jes1510/mendel_remix/parts/Cable_Chain/cc_150x8.stl

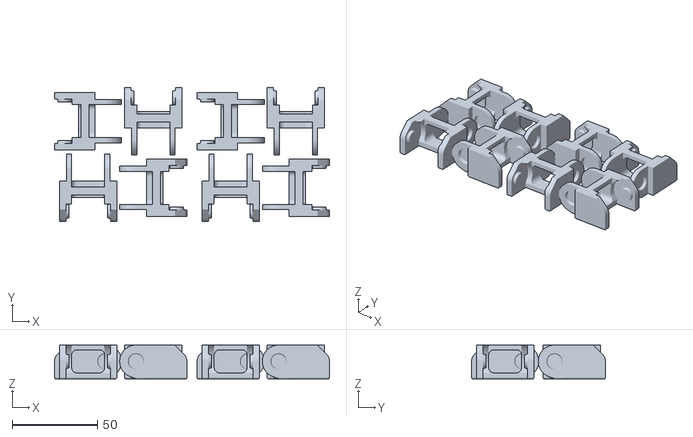
[picture p15: CAD file, 2015-03-10]
parts/Cable_Chain/cc_150x8.stl
161.2 x 78.5 x 19.9
