jes1510/mendel_remix/parts/case/Ramps_1.4_Mountable_Case/case_b.stl

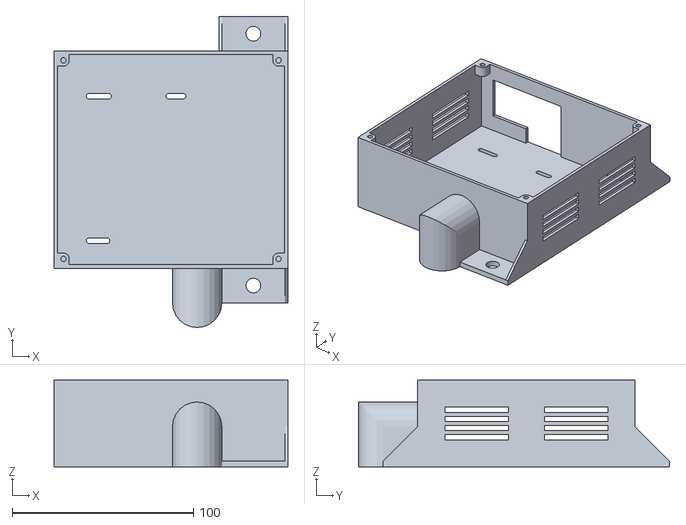
[picture p16: CAD file, 2015-03-10]
parts/case/Ramps_1.4_Mountable_Case/case_b.stl
129.1 x 171.8 x 48.0
