jes1510/mendel_remix/parts/electronics/Enclosure_RaspberryPi__ramps/Deckel_Fan.STL

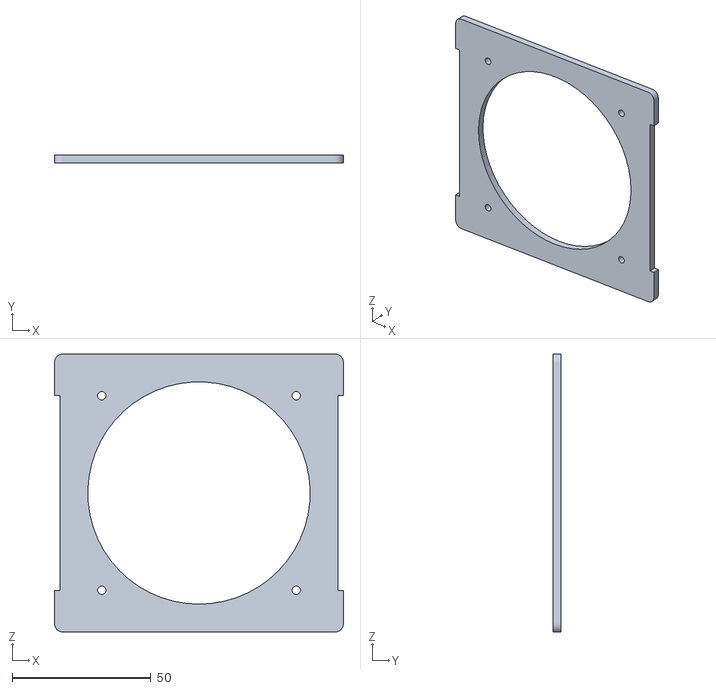
[picture p17: CAD file, 2014-10-29]
parts/electronics/Enclosure_RaspberryPi__ramps/Deckel_Fan.STL
104.0 x 3.00 x 100.0
