jes1510/mendel_remix/parts/enclosure/front_mid_brackets/front_mid_brackets_fixed.stl

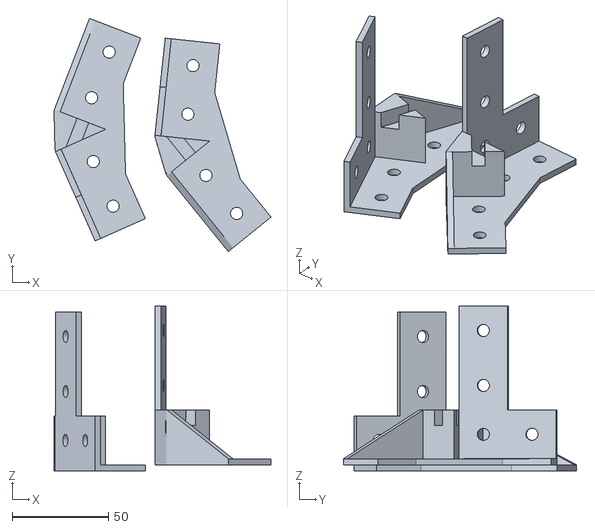
[picture p18: CAD file, 2015-06-04]
parts/enclosure/front_mid_brackets/front_mid_brackets_fixed.stl
112.8 x 121.3 x 85.7
