jes1510/mendel_remix/parts/enclosure/new_brackets/right_B_fixed.stl

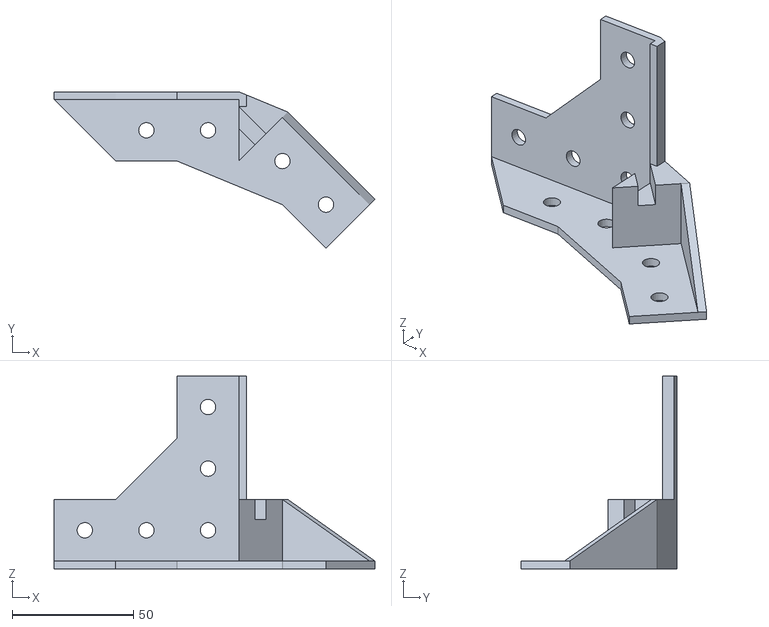
[picture p19: CAD file, 2015-06-04]
parts/enclosure/new_brackets/right_B_fixed.stl
132.3 x 64.5 x 79.4
