jes1510/mendel_remix/parts/enclosure/right_top_front_fixed.stl

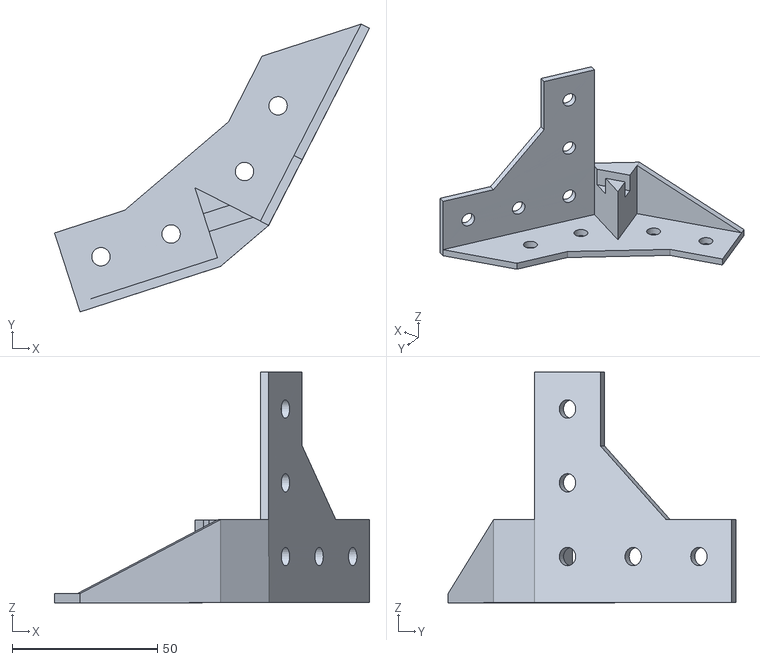
[picture p20: CAD file, 2015-06-04]
parts/enclosure/right_top_front_fixed.stl
108.5 x 99.1 x 79.4
