jes1510/mendel_remix/parts/enclosure/simple_brackets/sides_c.dxf

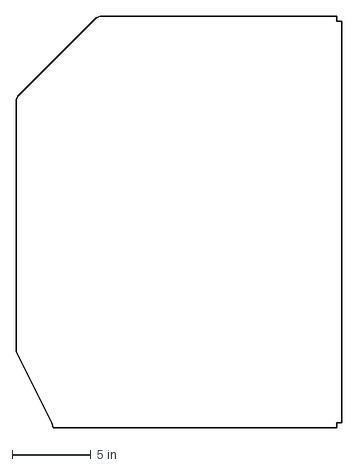
[picture p21: CAD file, 2015-06-04]
parts/enclosure/simple_brackets/sides_c.dxf
20.7 x 26.1 in
