jes1510/mendel_remix/parts/extruder_clamps.stl

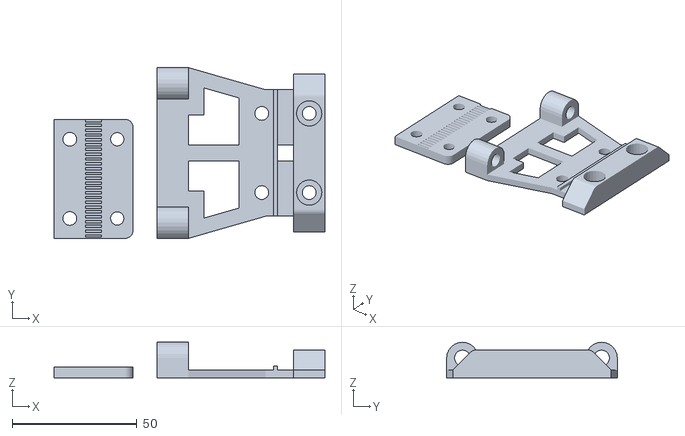
[picture p22: CAD file, 2015-03-10]
parts/extruder_clamps.stl
108.8 x 68.6 x 14.3
