jes1510/mendel_remix/parts/lcd_support/side.stl

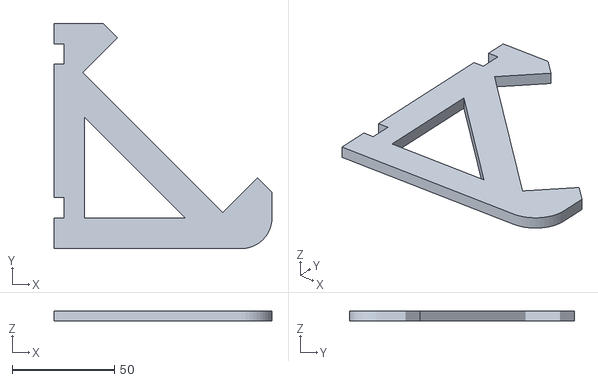
[picture p23: CAD file, 2014-11-15]
parts/lcd_support/side.stl
106.8 x 110.3 x 5.00
