jes1510/mendel_remix/parts/RAMP_14_Enclosure_Proven_to_fit/Case_Body.stl

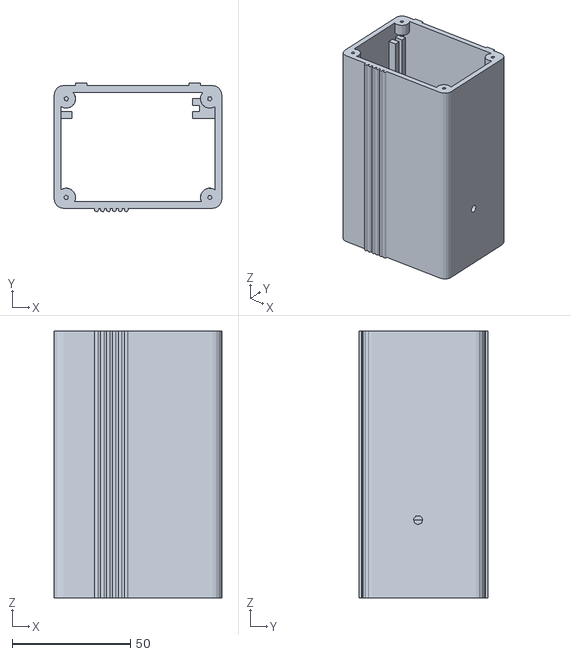
[picture p24: CAD file, 2014-11-15]
parts/RAMP_14_Enclosure_Proven_to_fit/Case_Body.stl
71.0 x 54.5 x 113.0
