jes1510/mendel_remix/xcablecarrier_brackets.dxf

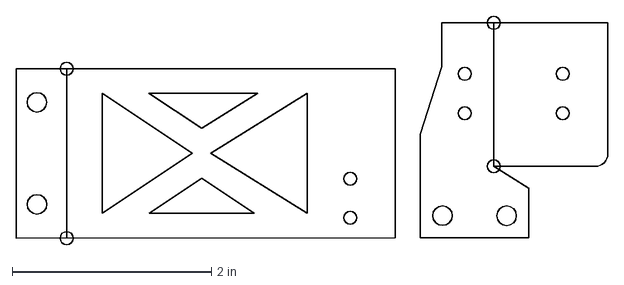
[picture p25: CAD file, 2015-03-10]
xcablecarrier_brackets.dxf
5.94 x 2.29 in
