jes1510/mendel_remix/parts/3DR_-_RepRapDiscount_Full_Graphic_Smart_Controller_case/3DR_Pablo_LCD_adapter.stl

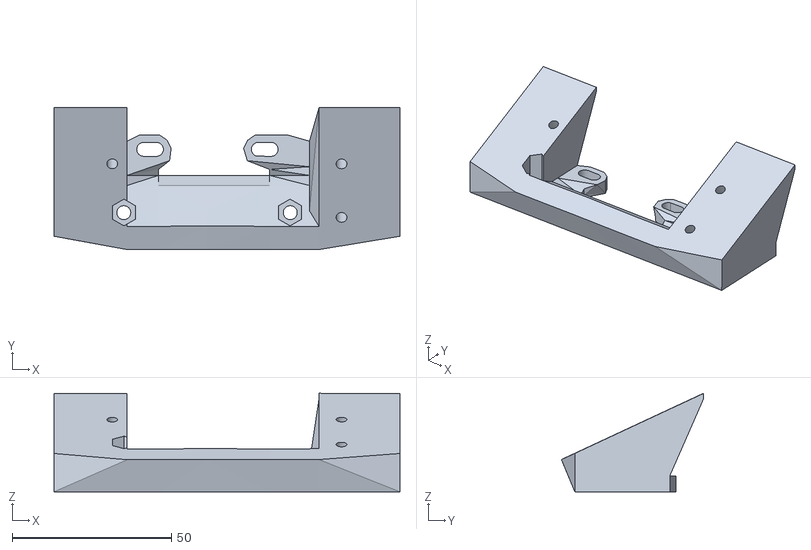
[picture p26: CAD file, 2014-11-15]
parts/3DR_-_RepRapDiscount_Full_Graphic_Smart_Controller_case/3DR_Pablo_LCD_adapter.stl
108.6 x 44.6 x 30.9
