jes1510/mendel_remix/parts/Cable_Chain/CableChainEnds.stl

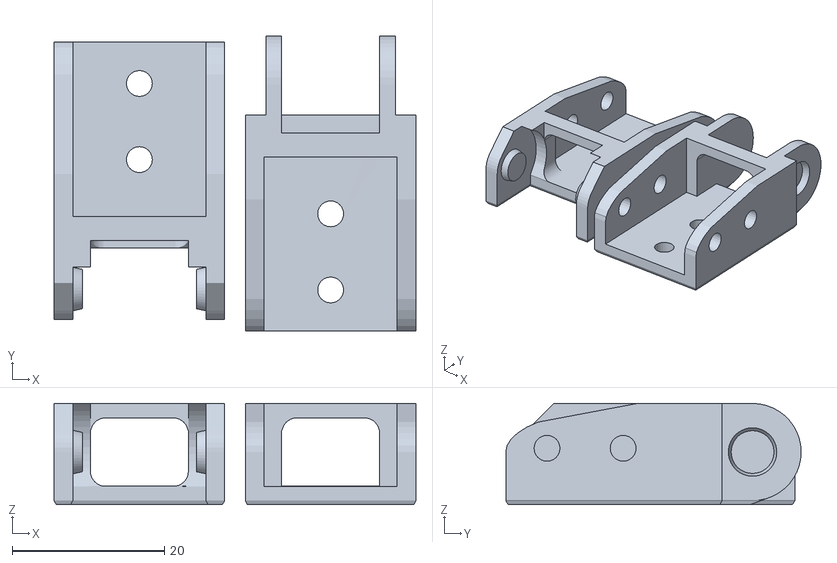
[picture p27: CAD file, 2014-11-15]
parts/Cable_Chain/CableChainEnds.stl
47.6 x 38.8 x 13.3
