jes1510/mendel_remix/parts/case/Ramps_1.4_Mountable_Case/Ramps_1.4_Mountable_Case06966831b87491ca3ae4c1595dea0038-Ramps_box_1-3_fan_cover.stl

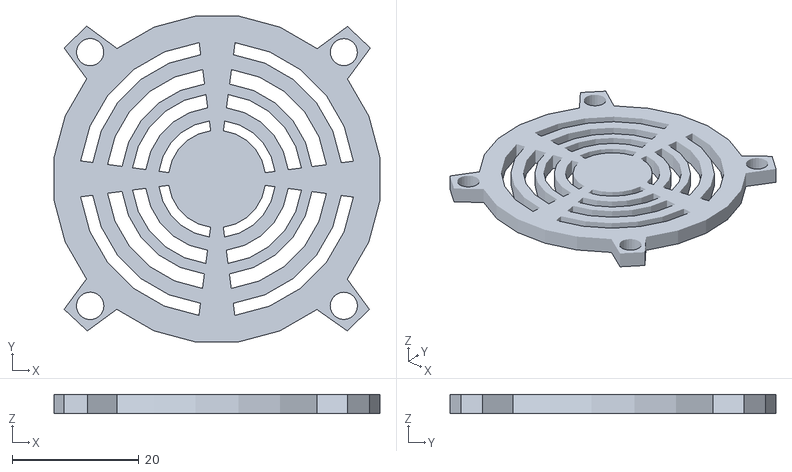
[picture p28: CAD file, 2015-03-10]
parts/case/Ramps_1.4_Mountable_Case/Ramps_1.4_Mountable_Case06966831b87491ca3ae4c1595dea0038-Ramps_box_1-3_fan_cover.stl
51.4 x 51.4 x 3.00
