jes1510/mendel_remix/parts/electronics/Enclosure_RaspberryPi__ramps/Schale.STL

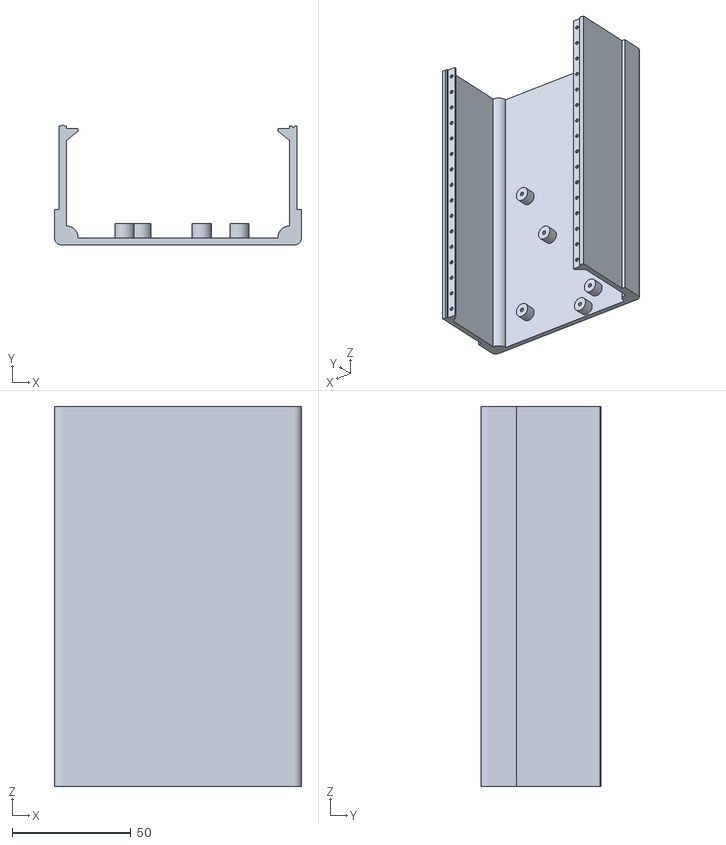
[picture p29: CAD file, 2014-10-29]
parts/electronics/Enclosure_RaspberryPi__ramps/Schale.STL
104.0 x 50.5 x 160.0
