jes1510/mendel_remix/parts/enclosure/front_mid_brackets/front_mid_L_Bracket.stl

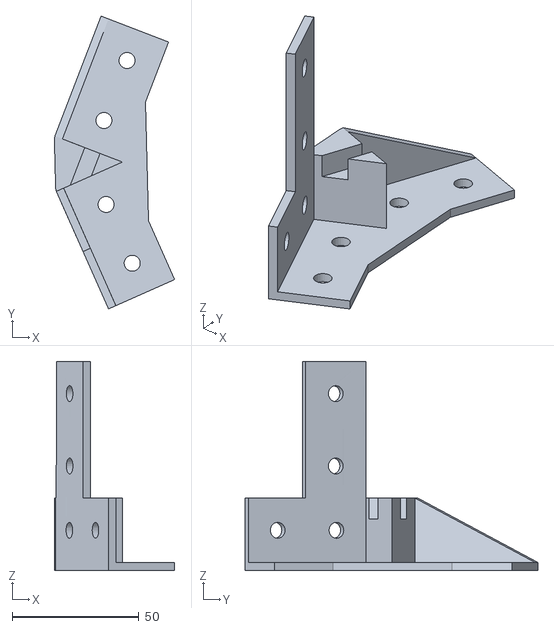
[picture p30: CAD file, 2015-06-04]
parts/enclosure/front_mid_brackets/front_mid_L_Bracket.stl
47.5 x 115.7 x 82.6
