jes1510/mendel_remix/parts/enclosure/new_brackets/right_A.stl

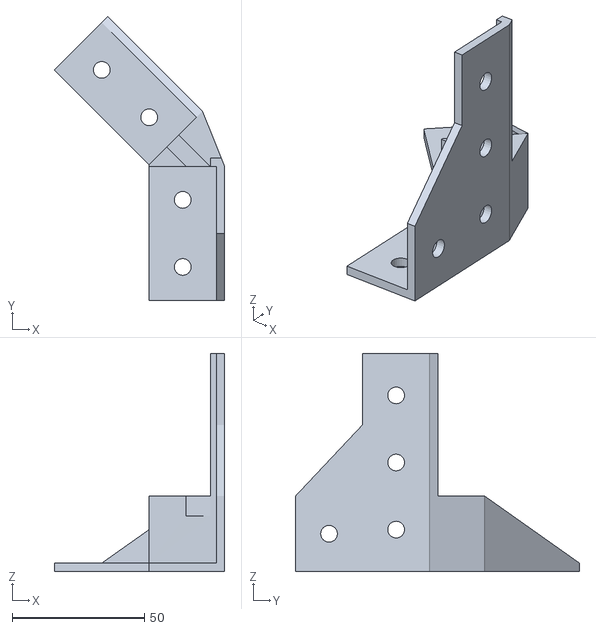
[picture p31: CAD file, 2015-06-04]
parts/enclosure/new_brackets/right_A.stl
64.5 x 107.5 x 82.6
