jes1510/mendel_remix/parts/enclosure/simple_brackets/sides.dxf

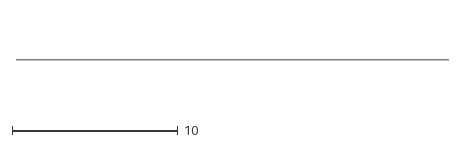
[picture p32: CAD file, 2015-06-04]
parts/enclosure/simple_brackets/sides.dxf
26.1 x 0.0455
