jes1510/mendel_remix/parts/enclosure/top_right.stl

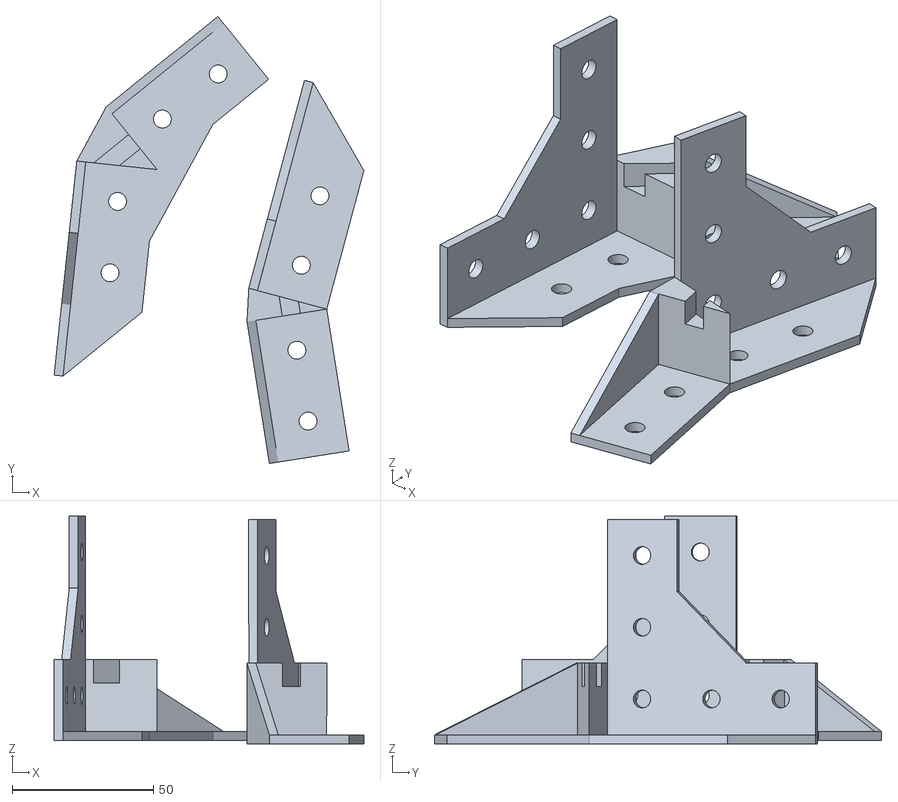
[picture p33: CAD file, 2015-06-04]
parts/enclosure/top_right.stl
109.6 x 158.2 x 80.6
