jes1510/mendel_remix/parts/lcd_support/bottom.stl

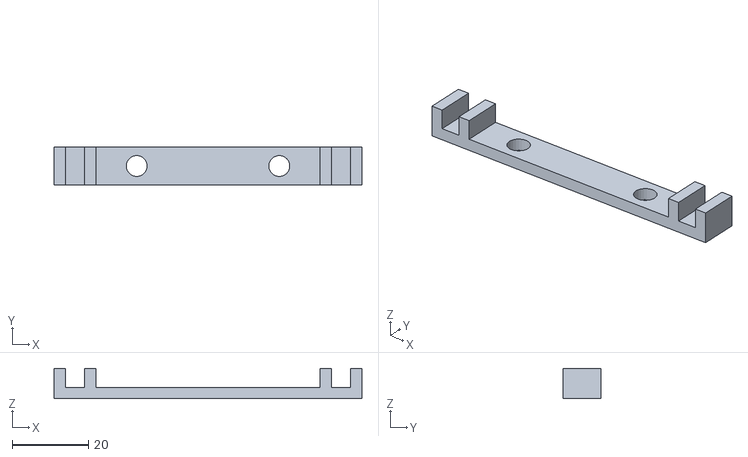
[picture p34: CAD file, 2014-11-15]
parts/lcd_support/bottom.stl
81.0 x 10.0 x 8.00
