jes1510/mendel_remix/parts/RAMP_14_Enclosure_Proven_to_fit/Right_Cover.stl

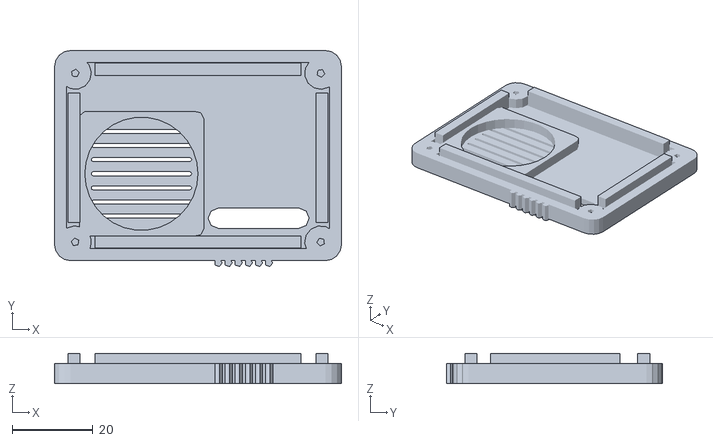
[picture p35: CAD file, 2014-11-15]
parts/RAMP_14_Enclosure_Proven_to_fit/Right_Cover.stl
71.0 x 53.5 x 7.50
