jes1510/mendel_remix/parts/wire_cover_b.stl

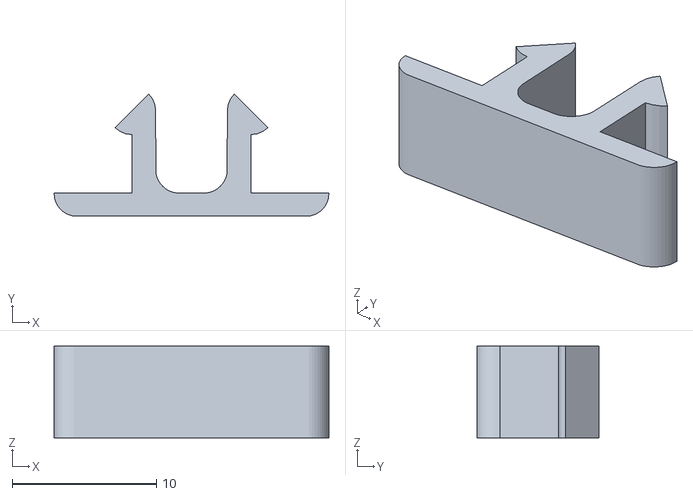
[picture p36: CAD file, 2015-03-10]
parts/wire_cover_b.stl
19.1 x 8.47 x 6.35
