jes1510/mendel_remix/y_tensioner.stl

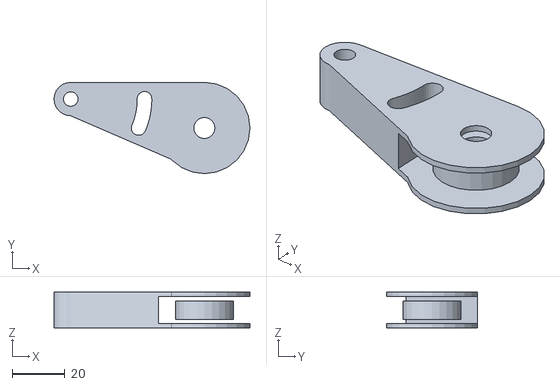
[picture p37: CAD file, 2014-10-29]
y_tensioner.stl
74.5 x 34.7 x 13.5
