jes1510/mendel_remix/parts/3DR_-_RepRapDiscount_Full_Graphic_Smart_Controller_case/3DR_Pablo_LCD_case_top.stl

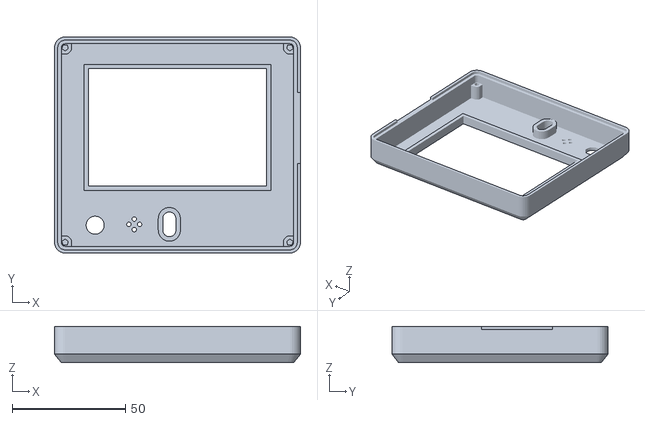
[picture p38: CAD file, 2014-11-15]
parts/3DR_-_RepRapDiscount_Full_Graphic_Smart_Controller_case/3DR_Pablo_LCD_case_top.stl
108.6 x 95.4 x 16.0
