jes1510/mendel_remix/parts/40mm_fab_extruder_bracket.dxf

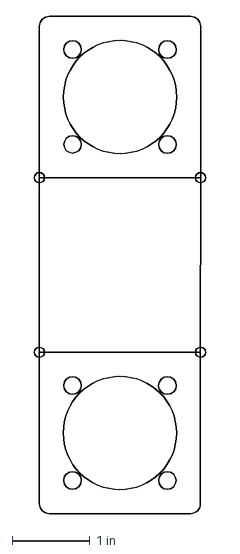
[picture p39: CAD file, 2015-03-10]
parts/40mm_fab_extruder_bracket.dxf
2.21 x 6.40 in
