jes1510/mendel_remix/parts/Cable_Chain/CableChainx4.stl

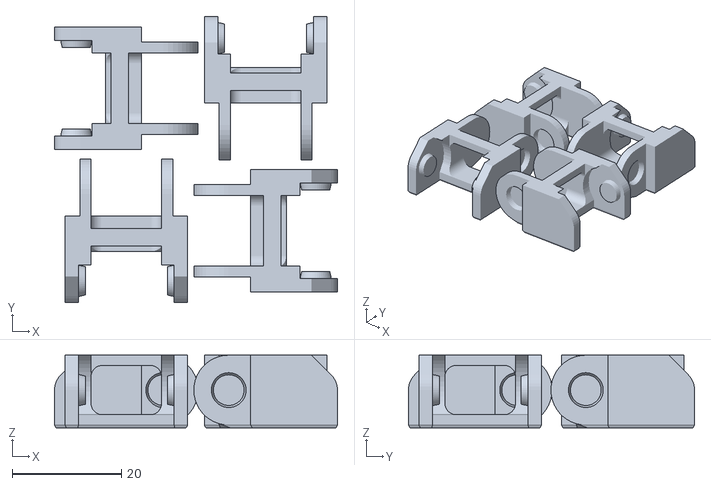
[picture p40: CAD file, 2014-11-15]
parts/Cable_Chain/CableChainx4.stl
51.7 x 52.3 x 13.3
