jes1510/mendel_remix/parts/case/Ramps_1.4_Mountable_Case/Ramps_1.4_Mountable_Case7d4c031f3561b140b59b32a3870bf5cb-Ramps_box_1-3__repaired_.stl

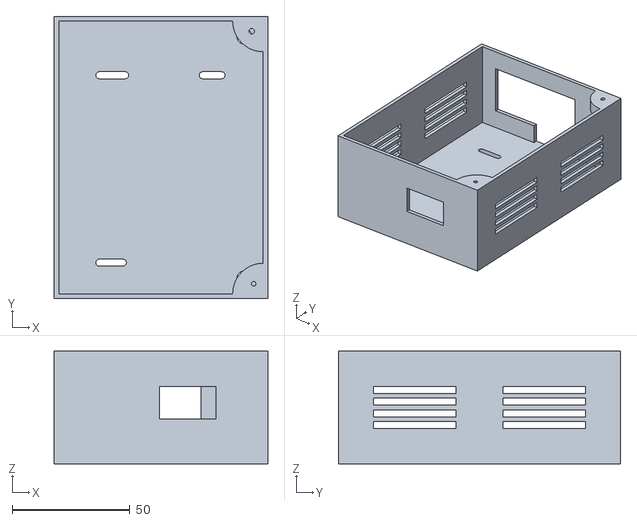
[picture p41: CAD file, 2015-03-10]
parts/case/Ramps_1.4_Mountable_Case/Ramps_1.4_Mountable_Case7d4c031f3561b140b59b32a3870bf5cb-Ramps_box_1-3__repaired_.stl
91.0 x 120.0 x 48.0
