jes1510/mendel_remix/parts/enclosure/bracket_set_plated_fixed.stl

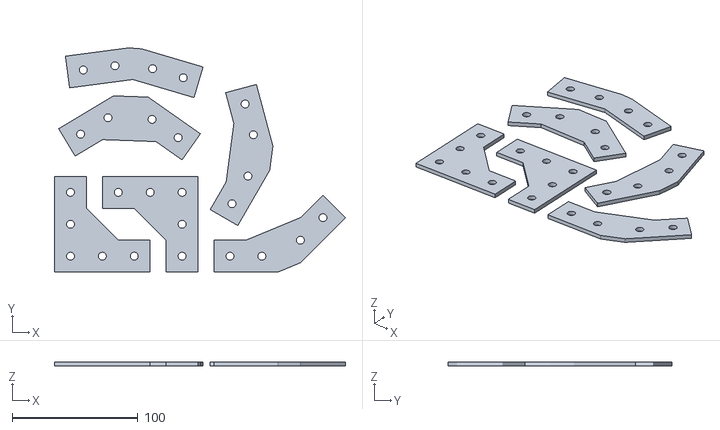
[picture p42: CAD file, 2015-06-04]
parts/enclosure/bracket_set_plated_fixed.stl
231.7 x 178.5 x 3.20
