jes1510/mendel_remix/parts/enclosure/new_brackets/left_a.stl

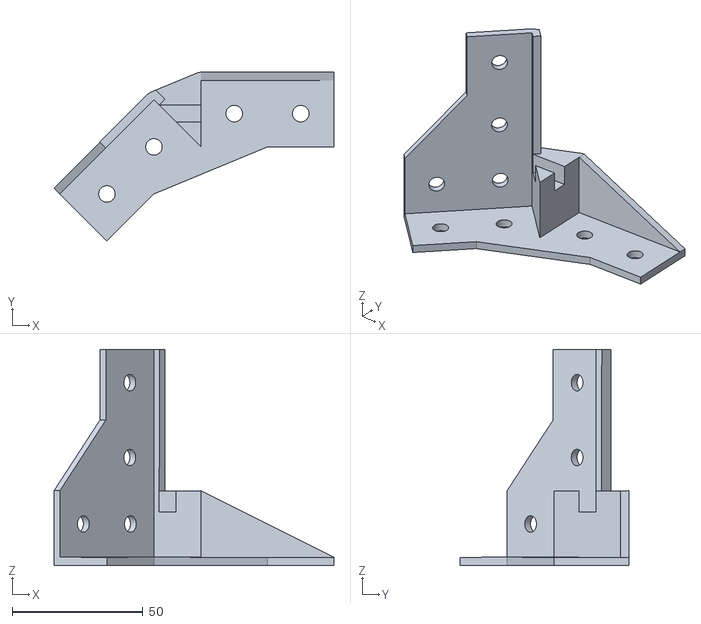
[picture p43: CAD file, 2015-06-04]
parts/enclosure/new_brackets/left_a.stl
106.9 x 64.5 x 82.6
