jes1510/mendel_remix/parts/enclosure/simple_brackets/1010_end_cutout.dxf

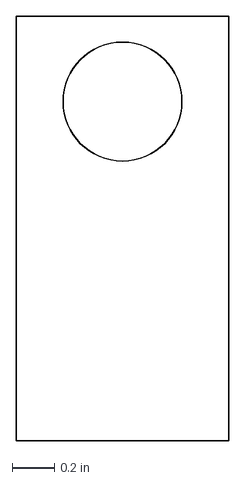
[picture p44: CAD file, 2015-06-04]
parts/enclosure/simple_brackets/1010_end_cutout.dxf
1.00 x 2.00 in
