jes1510/mendel_remix/table.dxf

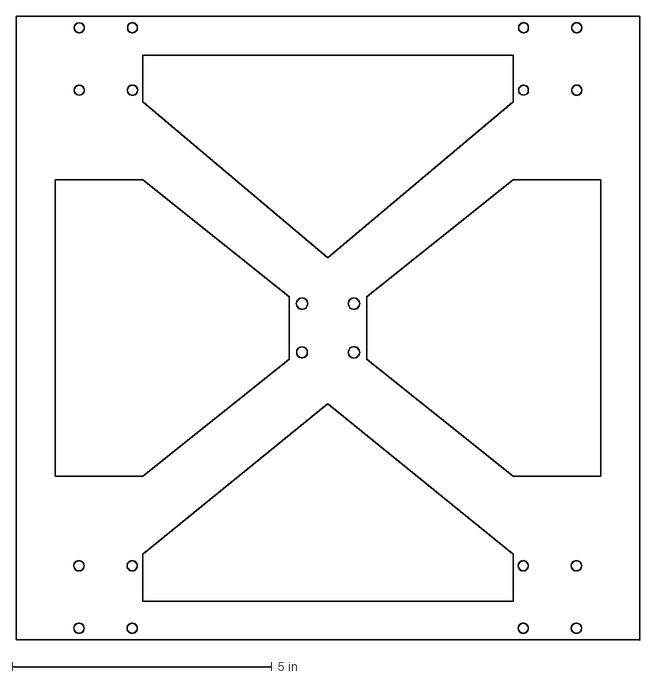
[picture p46: CAD file, 2014-10-29]
table.dxf
12.0 x 12.0 in
