jes1510/mendel_remix/L_Bracket.dxf

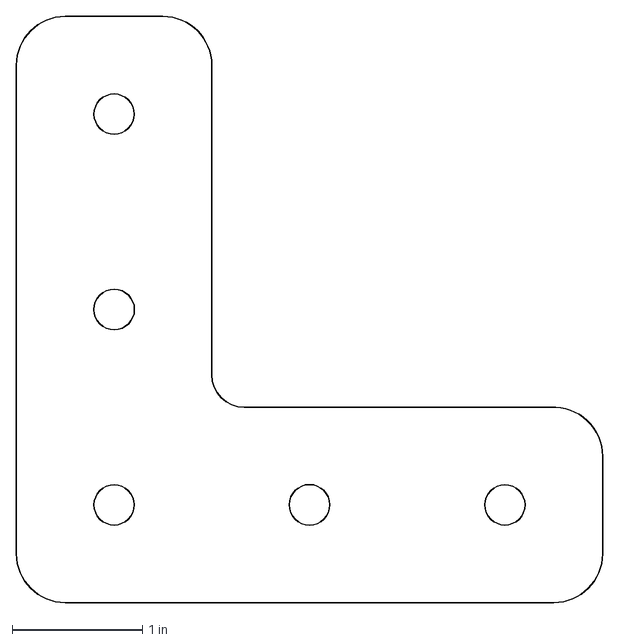
[picture p47: CAD file, 2014-10-29]
L_Bracket.dxf
4.50 x 4.50 in
