jes1510/mendel_remix/parts/3DR_-_RepRapDiscount_Full_Graphic_Smart_Controller_case/3DR_Pablo_LCD_button_big.stl

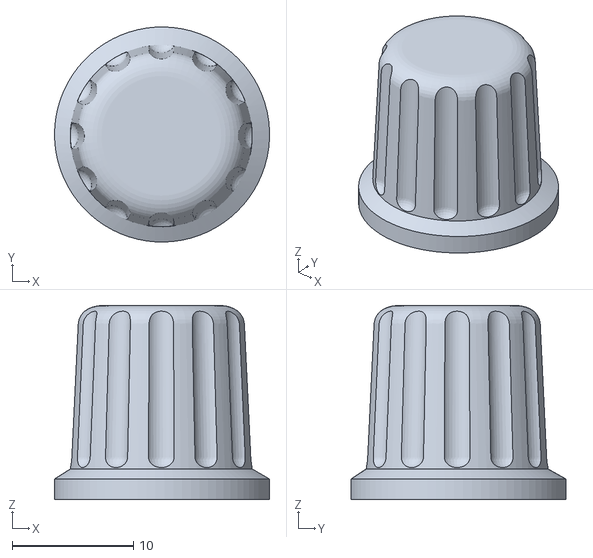
[picture p48: CAD file, 2014-11-15]
parts/3DR_-_RepRapDiscount_Full_Graphic_Smart_Controller_case/3DR_Pablo_LCD_button_big.stl
17.7 x 17.7 x 16.0
