jes1510/mendel_remix/parts/Cable_Chain/CableChain.stl

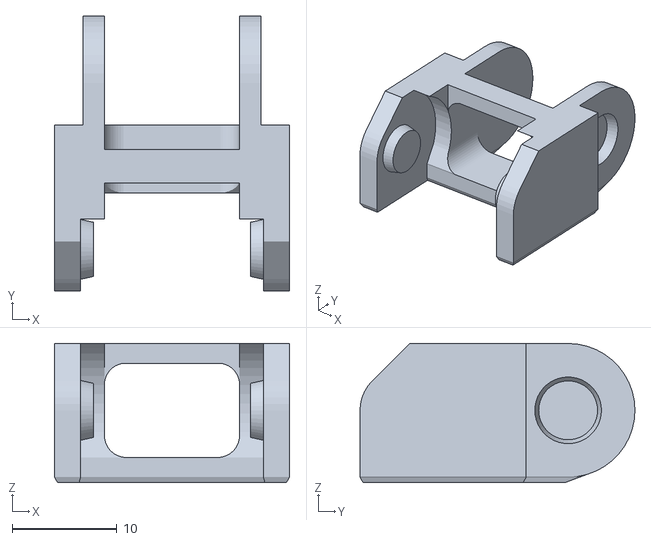
[picture p49: CAD file, 2014-11-15]
parts/Cable_Chain/CableChain.stl
22.4 x 26.3 x 13.3
