jes1510/mendel_remix/parts/enclosure/right_angle_braqckets.stl

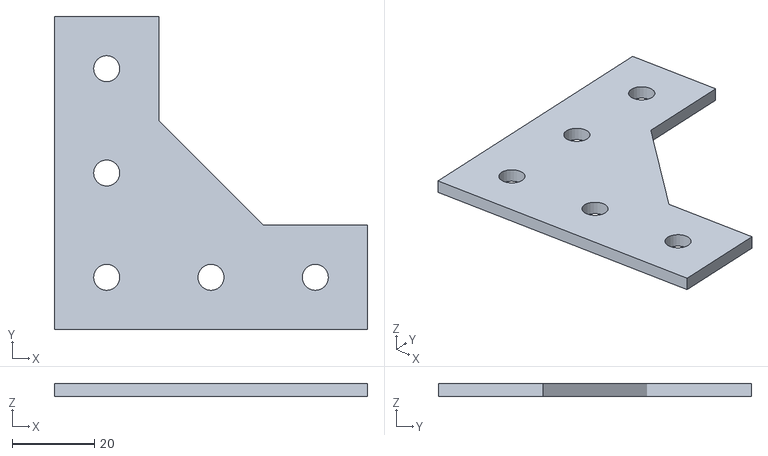
[picture p50: CAD file, 2015-06-04]
parts/enclosure/right_angle_braqckets.stl
76.2 x 76.2 x 3.18
