jes1510/mendel_remix/parts/enclosure/simple_brackets/side_quarter_panels.dxf

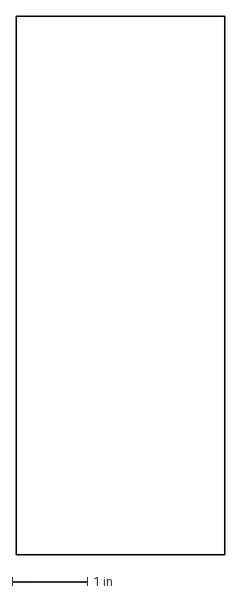
[picture p51: CAD file, 2015-06-04]
parts/enclosure/simple_brackets/side_quarter_panels.dxf
2.77 x 7.15 in
