jes1510/mendel_remix/parts/wire_clip_c.stl

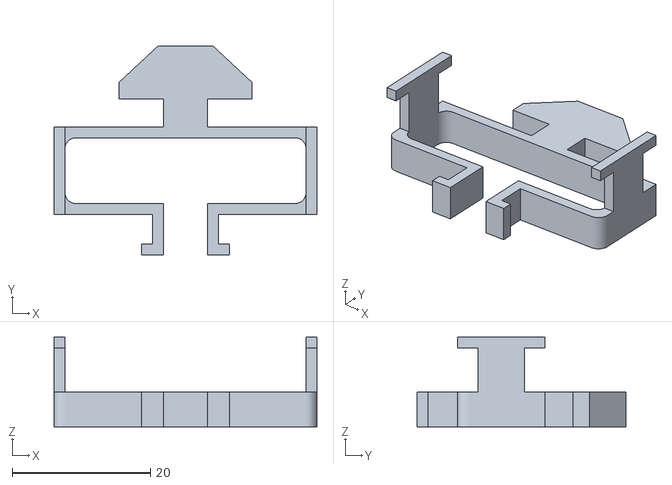
[picture p52: CAD file, 2015-03-10]
parts/wire_clip_c.stl
38.1 x 30.2 x 13.0
