jes1510/mendel_remix/extruder_car_bc.stl

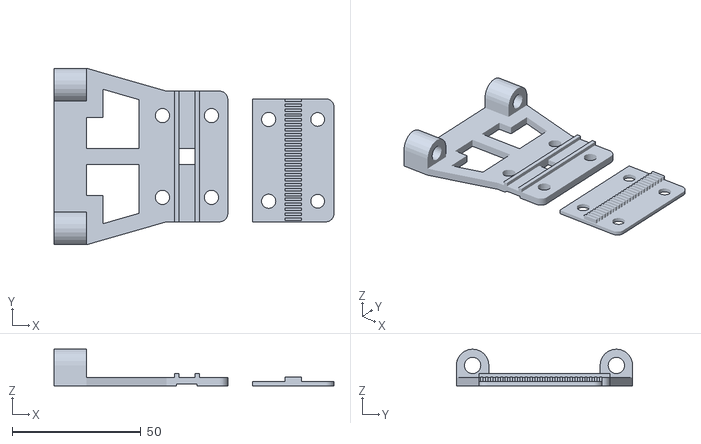
[picture p53: CAD file, 2014-10-29]
extruder_car_bc.stl
108.8 x 68.6 x 14.3
