jes1510/mendel_remix/parts/3DR_-_RepRapDiscount_Full_Graphic_Smart_Controller_case/3DR_Pablo_LCD_distance_cylinder.stl

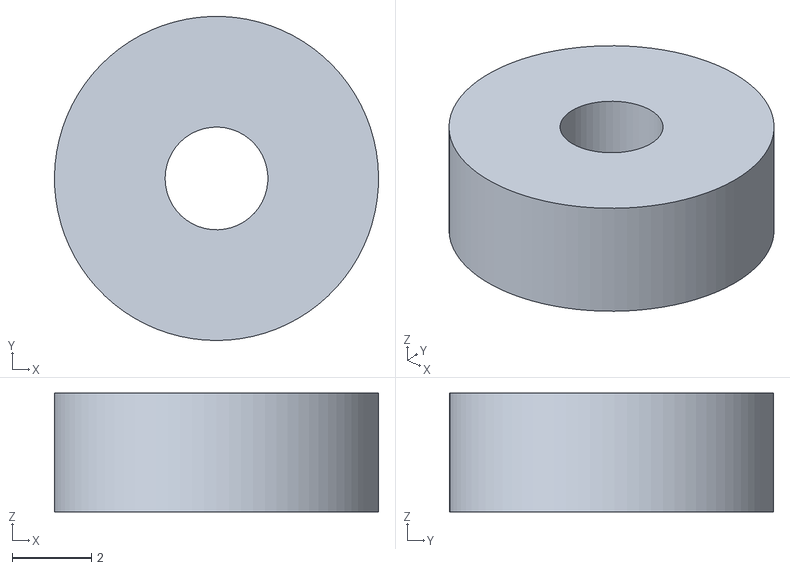
[picture p54: CAD file, 2014-11-15]
parts/3DR_-_RepRapDiscount_Full_Graphic_Smart_Controller_case/3DR_Pablo_LCD_distance_cylinder.stl
8.20 x 8.20 x 3.00
