jes1510/mendel_remix/parts/Cable_Chain/CenterCal.stl

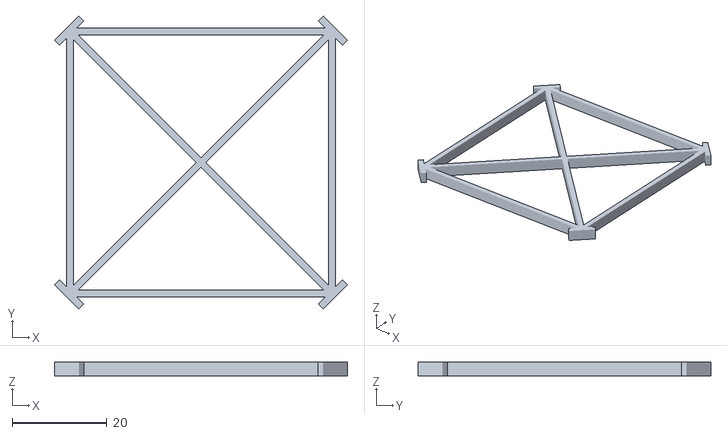
[picture p55: CAD file, 2014-11-15]
parts/Cable_Chain/CenterCal.stl
61.7 x 61.7 x 3.00
