jes1510/mendel_remix/parts/case/Ramps_1.4_Mountable_Case/lid.stl

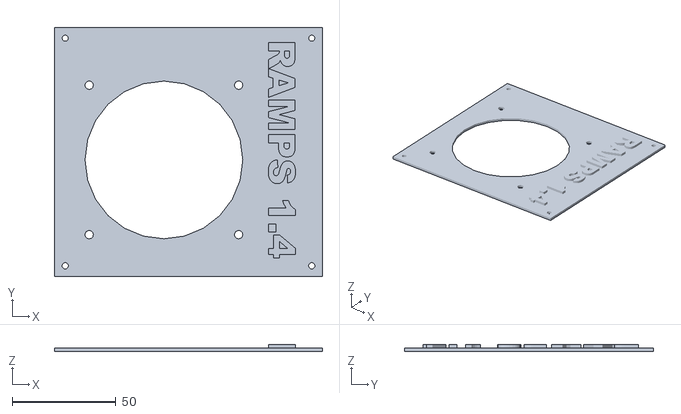
[picture p56: CAD file, 2015-03-10]
parts/case/Ramps_1.4_Mountable_Case/lid.stl
129.1 x 120.0 x 3.37
