jes1510/mendel_remix/parts/enclosure/simple_brackets/sides_b.dxf

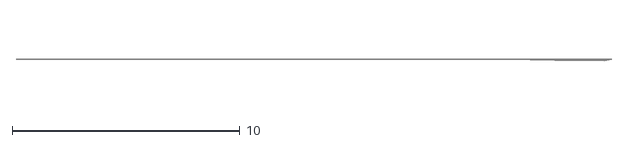
[picture p58: CAD file, 2015-06-04]
parts/enclosure/simple_brackets/sides_b.dxf
26.1 x 0.0455
