jes1510/mendel_remix/parts/wire_cover.stl

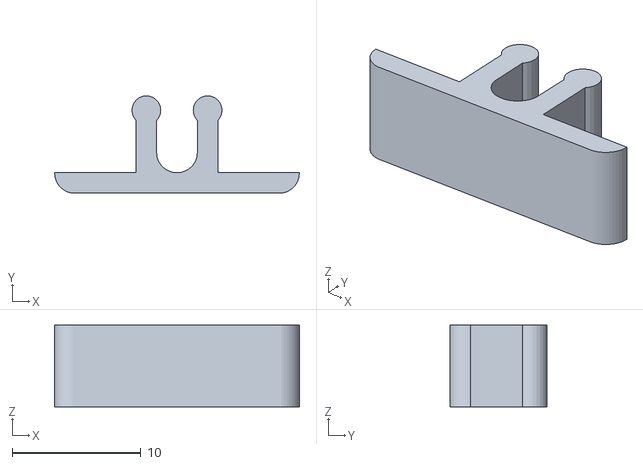
[picture p59: CAD file, 2015-03-10]
parts/wire_cover.stl
19.1 x 7.57 x 6.35
