jes1510/mendel_remix/parts/case/Ramps_1.4_Mountable_Case/Ramps_1.4_Mountable_Case2085ba616779a3938224605bac95cc47-Ramps_box_1-3_top.stl

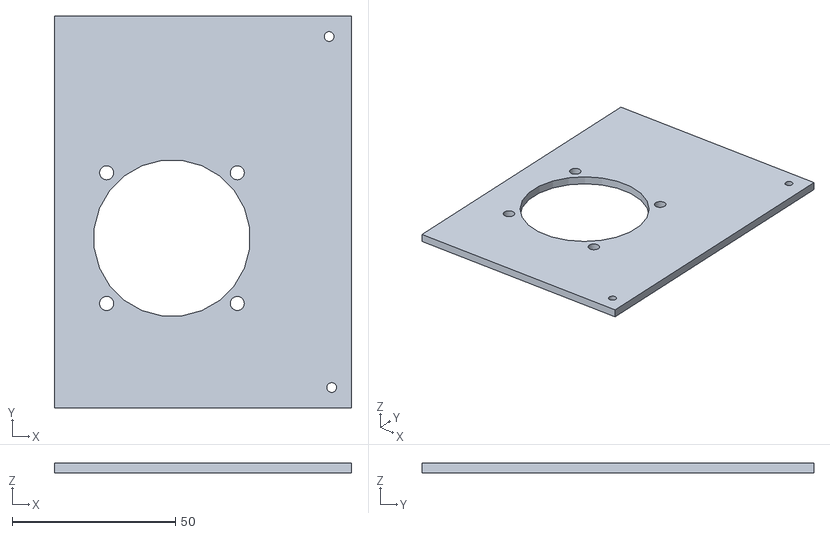
[picture p60: CAD file, 2015-03-10]
parts/case/Ramps_1.4_Mountable_Case/Ramps_1.4_Mountable_Case2085ba616779a3938224605bac95cc47-Ramps_box_1-3_top.stl
91.0 x 120.0 x 3.00
