jes1510/mendel_remix/parts/enclosure/l_bracket_x6.dxf

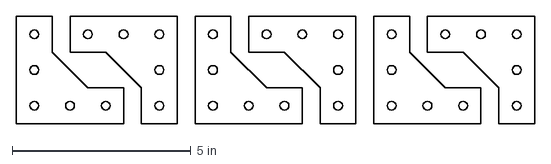
[picture p61: CAD file, 2015-06-04]
parts/enclosure/l_bracket_x6.dxf
14.5 x 3.00 in
