jes1510/mendel_remix/parts/enclosure/simple_brackets/panel_top_back.dxf

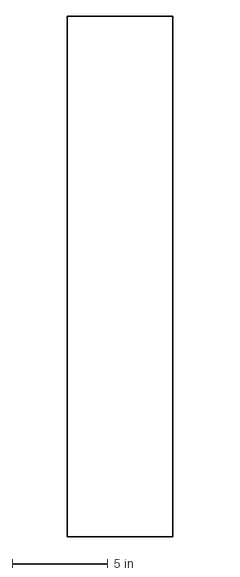
[picture p62: CAD file, 2015-06-04]
parts/enclosure/simple_brackets/panel_top_back.dxf
5.50 x 27.1 in
