jes1510/mendel_remix/parts/wire_clip.stl

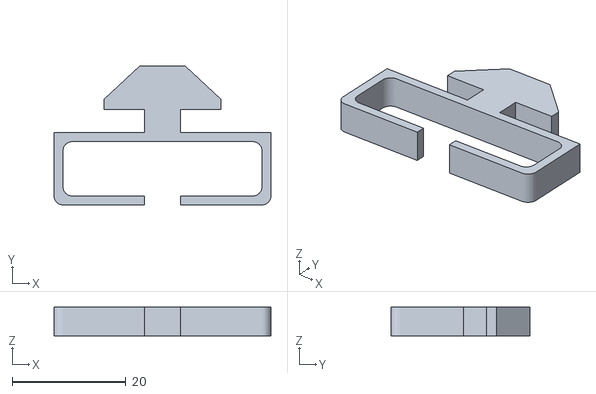
[picture p63: CAD file, 2015-03-10]
parts/wire_clip.stl
38.1 x 24.4 x 5.08
