jes1510/mendel_remix/table_belt_attachment.stl

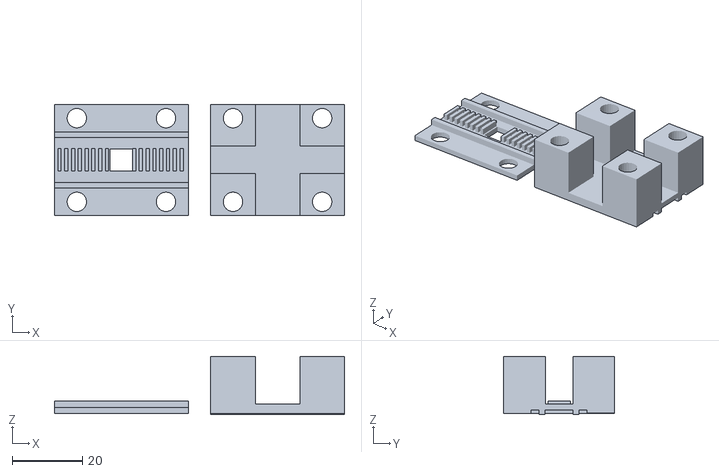
[picture p64: CAD file, 2014-10-29]
table_belt_attachment.stl
82.6 x 31.8 x 16.5
