jes1510/mendel_remix/front_back_b.dxf

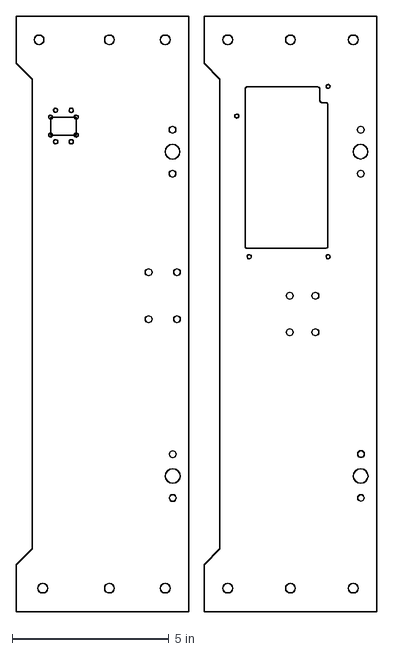
[picture p65: CAD file, 2014-10-29]
front_back_b.dxf
11.5 x 19.0 in
