jes1510/mendel_remix/parts/8020_angle_bracket.stl

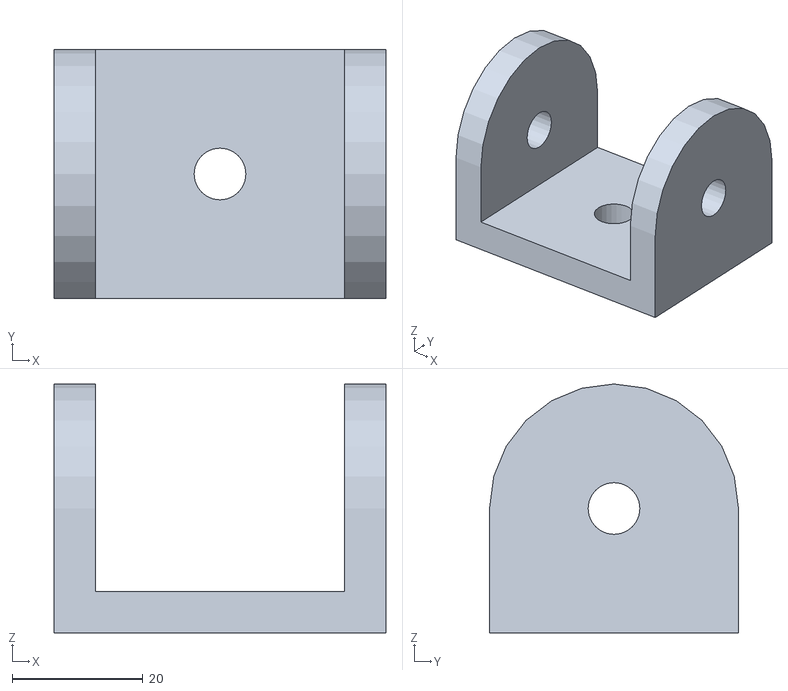
[picture p66: CAD file, 2014-11-15]
parts/8020_angle_bracket.stl
50.8 x 38.1 x 38.1
