jes1510/mendel_remix/extruder_carriage_b.stl

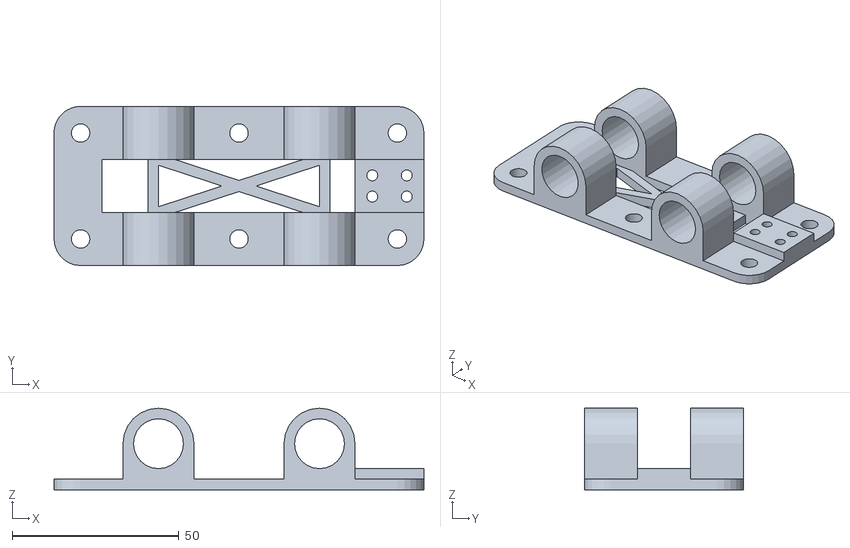
[picture p67: CAD file, 2014-10-29]
extruder_carriage_b.stl
111.1 x 47.8 x 24.5
