jes1510/mendel_remix/parts/enclosure/L_Bracket.dxf

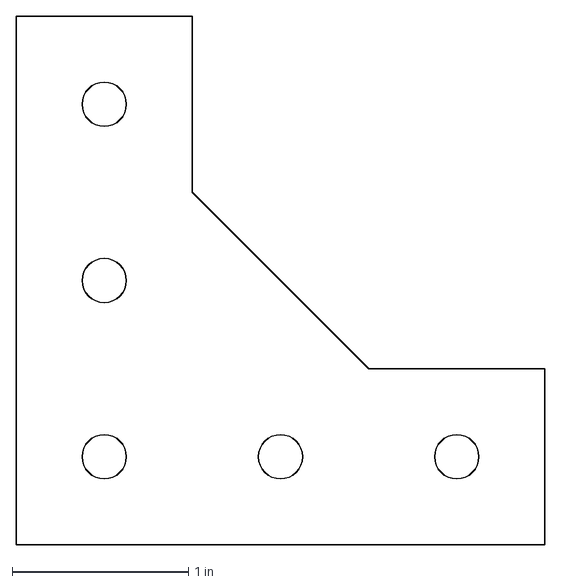
[picture p68: CAD file, 2015-06-04]
parts/enclosure/L_Bracket.dxf
3.00 x 3.00 in
