jes1510/mendel_remix/parts/foot_cover.stl

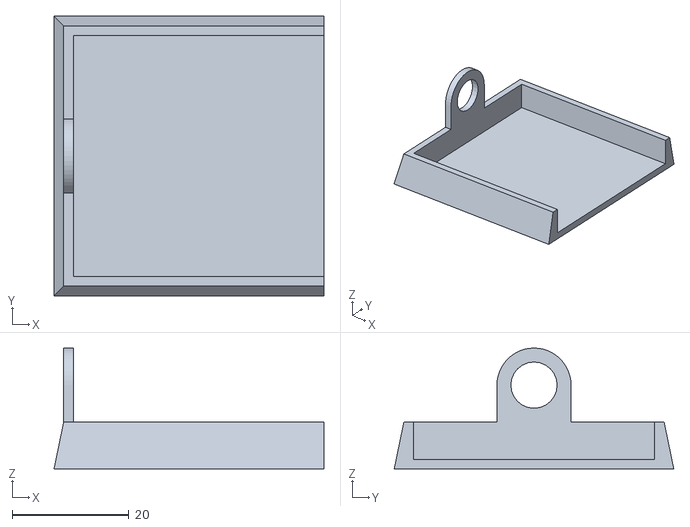
[picture p69: CAD file, 2014-11-03]
parts/foot_cover.stl
46.2 x 47.9 x 20.7
