jes1510/mendel_remix/parts/bed_leveler_bracket.dxf

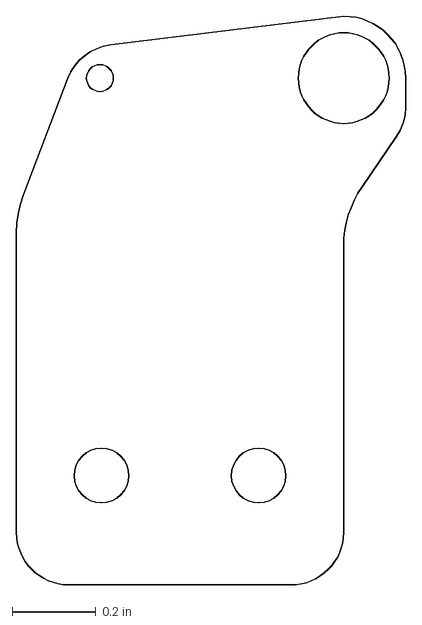
[picture p70: CAD file, 2014-10-29]
parts/bed_leveler_bracket.dxf
0.928 x 1.36 in
