jes1510/mendel_remix/tensioner.dxf

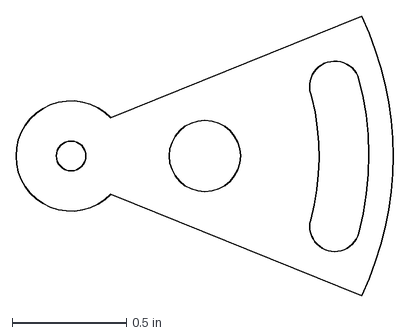
[picture p71: CAD file, 2014-10-29]
tensioner.dxf
1.70 x 1.22 in
