jes1510/mendel_remix/parts/endstops_brackets_nested.dxf

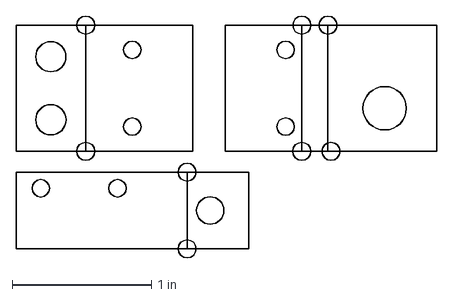
[picture p72: CAD file, 2014-10-29]
parts/endstops_brackets_nested.dxf
3.02 x 1.74 in
