jes1510/mendel_remix/vertical_support.dxf

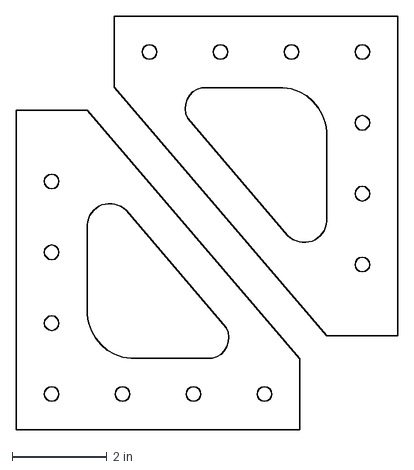
[picture p73: CAD file, 2014-10-29]
vertical_support.dxf
8.07 x 8.74 in
