jes1510/mendel_remix/brackets.dxf

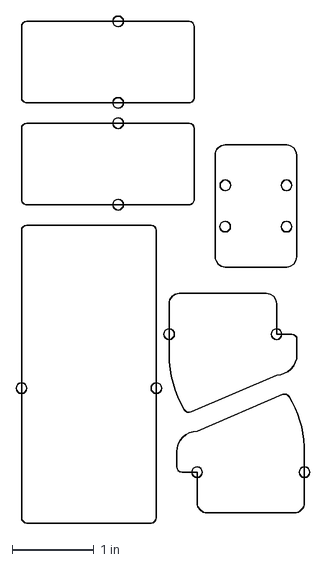
[picture p74: CAD file, 2014-10-29]
brackets.dxf
3.60 x 6.22 in
