jes1510/mendel_remix/parts/endstop_bracket_x_flat.dxf

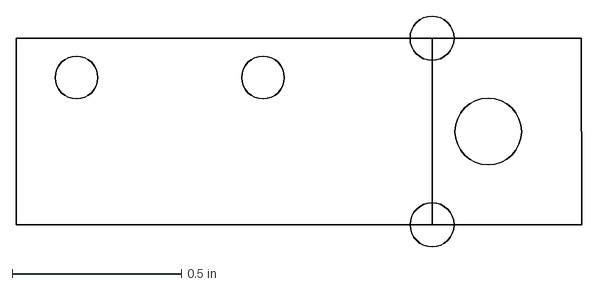
[picture p75: CAD file, 2014-10-29]
parts/endstop_bracket_x_flat.dxf
1.67 x 0.681 in
