jes1510/mendel_remix/bottom_z_support.dxf

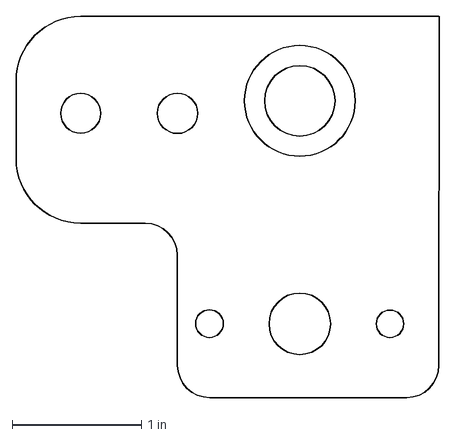
[picture p76: CAD file, 2014-10-29]
bottom_z_support.dxf
3.27 x 2.95 in
