jes1510/mendel_remix/parts/endstop_bracket_y_flat.dxf

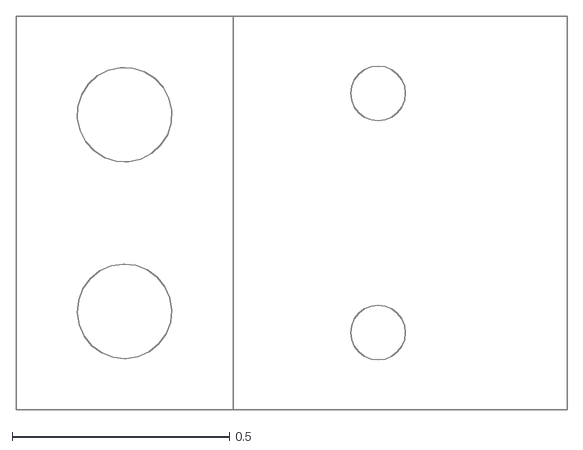
[picture p77: CAD file, 2014-10-29]
parts/endstop_bracket_y_flat.dxf
1.27 x 0.906
