jes1510/mendel_remix/Lbracket_support_nested.dxf

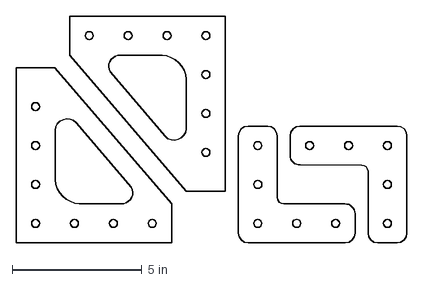
[picture p78: CAD file, 2014-10-29]
Lbracket_support_nested.dxf
15.1 x 8.74 in
