jes1510/mendel_remix/parts/extruder_support_bracket_flat.dxf

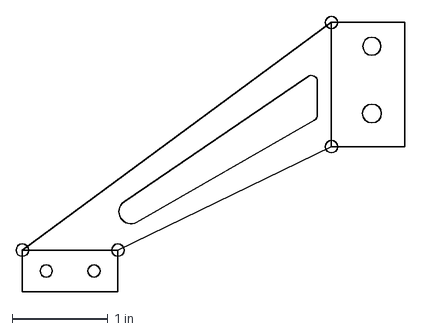
[picture p79: CAD file, 2014-10-29]
parts/extruder_support_bracket_flat.dxf
4.07 x 2.88 in
