jes1510/mendel_remix/parts/box.dxf

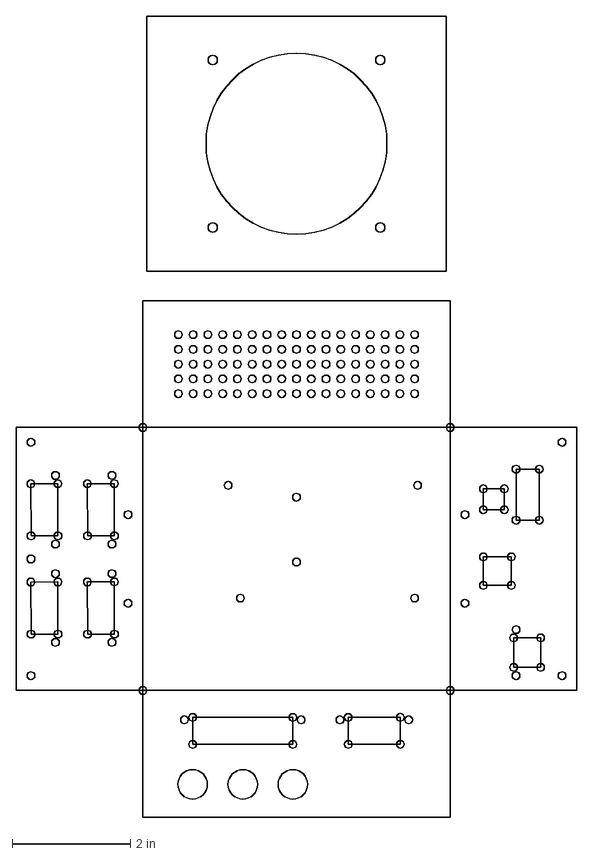
[picture p80: CAD file, 2014-10-29]
parts/box.dxf
9.49 x 13.6 in
