jes1510/mendel_remix/smooth_bottom.dxf

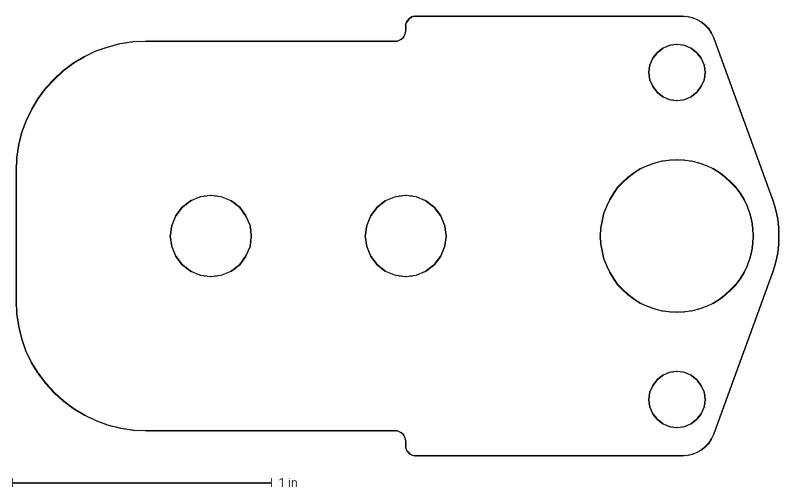
[picture p81: CAD file, 2014-10-29]
smooth_bottom.dxf
2.94 x 1.69 in
