jes1510/mendel_remix/motor_spacer.dxf

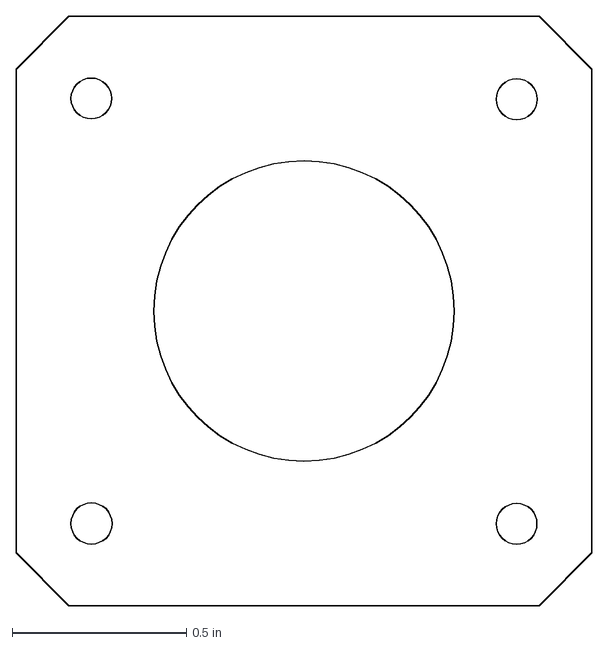
[picture p82: CAD file, 2014-10-29]
motor_spacer.dxf
1.65 x 1.69 in
