jes1510/mendel_remix/parts/endstop_bracket_z_flat.dxf

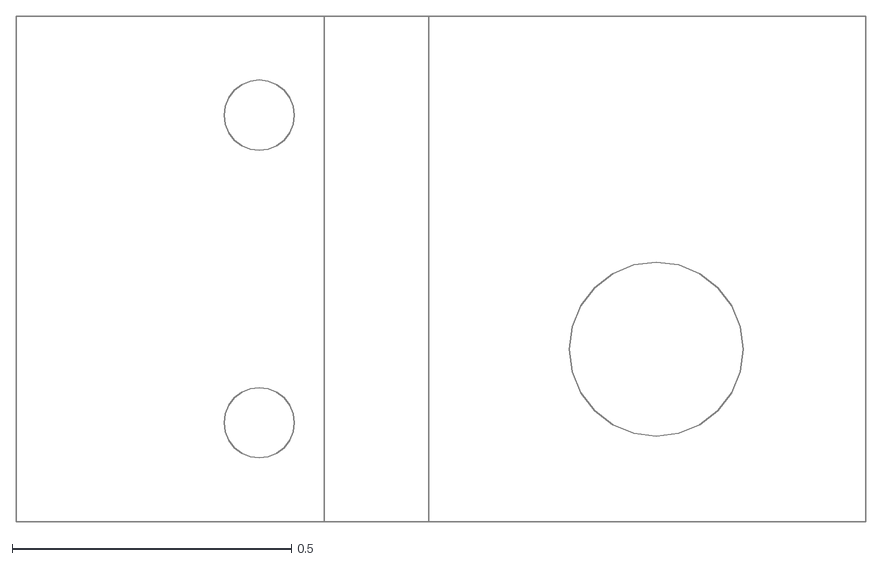
[picture p83: CAD file, 2014-10-29]
parts/endstop_bracket_z_flat.dxf
1.52 x 0.906
