jes1510/mendel_remix/parts/spacer_blocks_nested.dxf

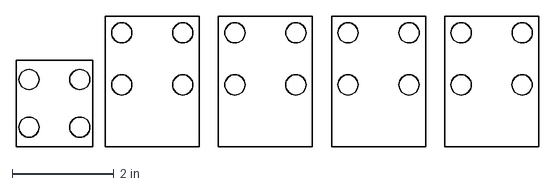
[picture p85: CAD file, 2014-10-29]
parts/spacer_blocks_nested.dxf
10.3 x 2.56 in
