jes1510/mendel_remix/slide_holder.dxf

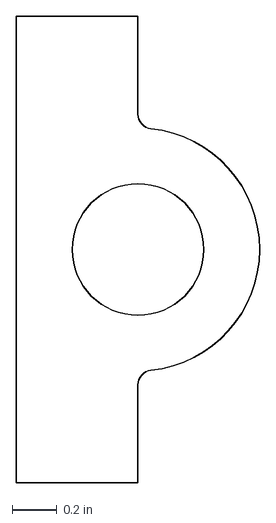
[picture p86: CAD file, 2014-10-29]
slide_holder.dxf
1.09 x 2.09 in
