jes1510/mendel_remix/extruder_bracket_b.dxf

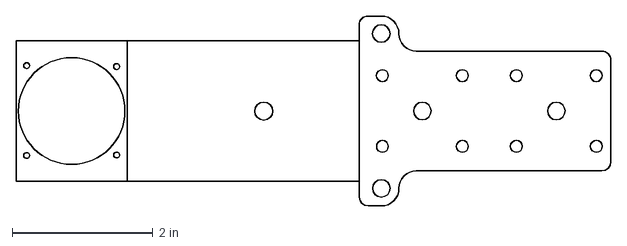
[picture p87: CAD file, 2014-10-29]
extruder_bracket_b.dxf
8.45 x 2.70 in
