jes1510/mendel_remix/x_carriage_left.dxf

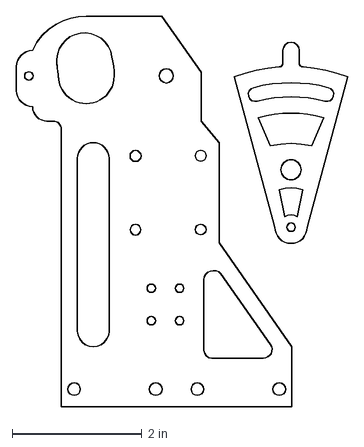
[picture p88: CAD file, 2014-10-29]
x_carriage_left.dxf
5.11 x 6.03 in
