jes1510/mendel_remix/extruder_carriage_c_print.stl

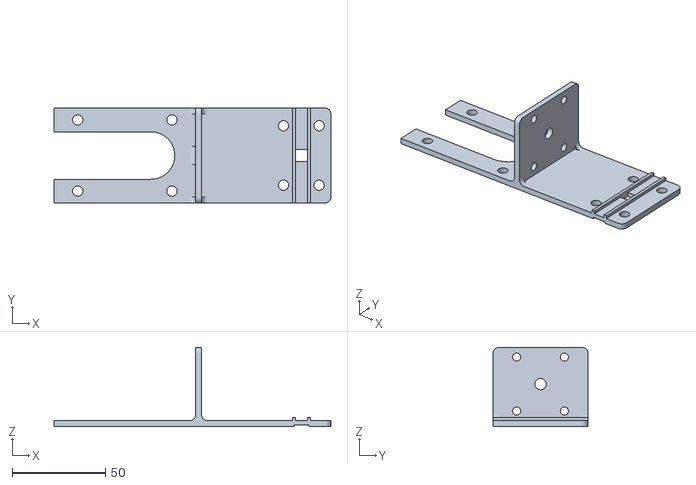
[picture p89: CAD file, 2014-10-29]
extruder_carriage_c_print.stl
148.2 x 50.8 x 42.4
