jes1510/mendel_remix/z_motor_mount.dxf

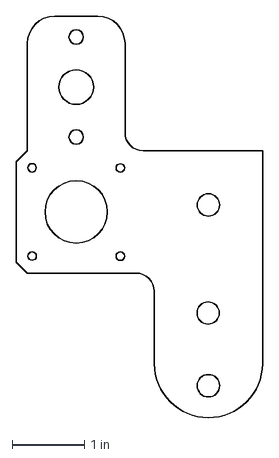
[picture p90: CAD file, 2014-10-29]
z_motor_mount.dxf
3.40 x 5.55 in
