jes1510/mendel_remix/brackets_b.dxf

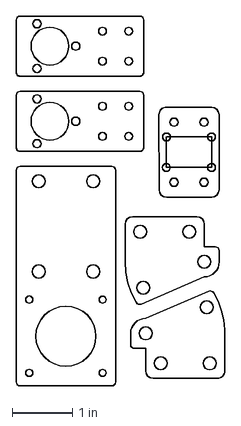
[picture p91: CAD file, 2014-10-29]
brackets_b.dxf
3.47 x 6.15 in
