jes1510/mendel_remix/tensioner_bracket_b.dxf

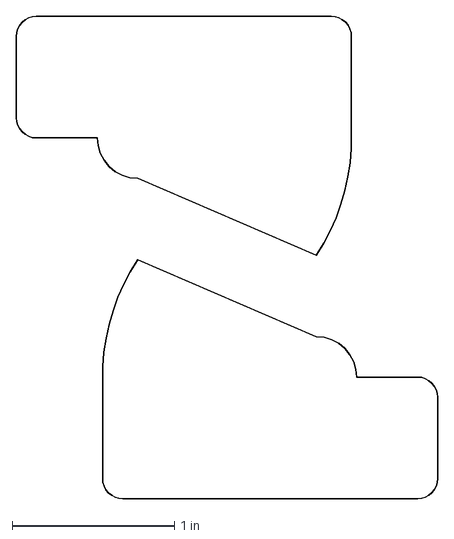
[picture p92: CAD file, 2014-10-29]
tensioner_bracket_b.dxf
2.60 x 2.97 in
