jes1510/mendel_remix/extruder_carriage.stl

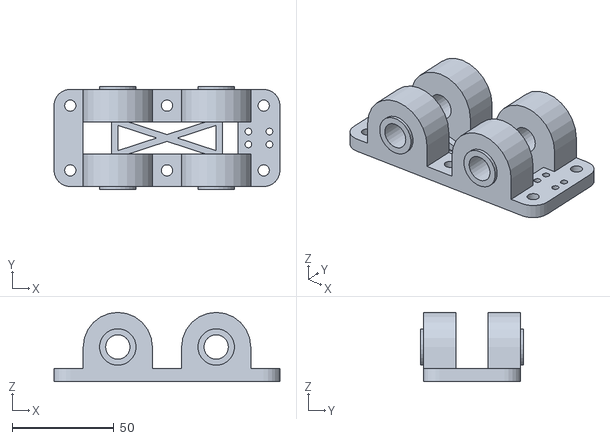
[picture p93: CAD file, 2014-10-29]
extruder_carriage.stl
111.1 x 50.8 x 34.0
