jes1510/mendel_remix/endstop_brackets_nested.dxf

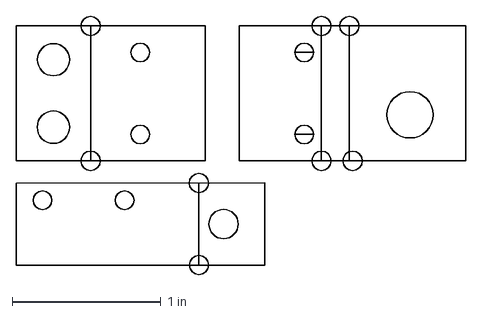
[picture p94: CAD file, 2014-10-29]
endstop_brackets_nested.dxf
3.02 x 1.74 in
