jes1510/mendel_remix/fron_back_panels.dxf

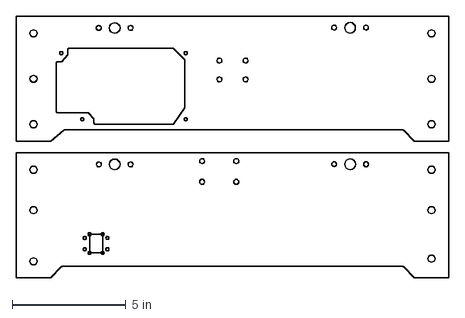
[picture p95: CAD file, 2014-10-29]
fron_back_panels.dxf
19.0 x 11.5 in
