jes1510/mendel_remix/motor_extruder_bracket.dxf

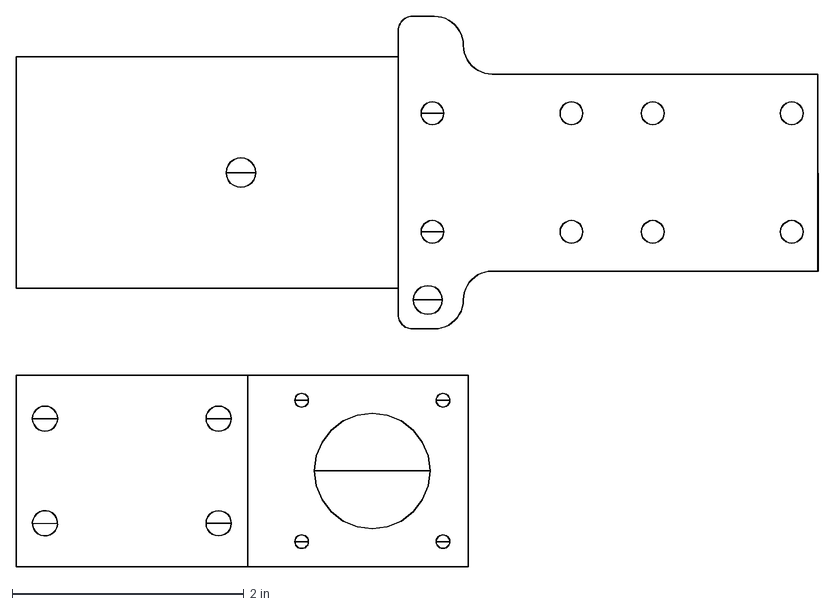
[picture p96: CAD file, 2014-10-29]
motor_extruder_bracket.dxf
6.93 x 4.75 in
