jes1510/mendel_remix/extruder_bracket.dxf

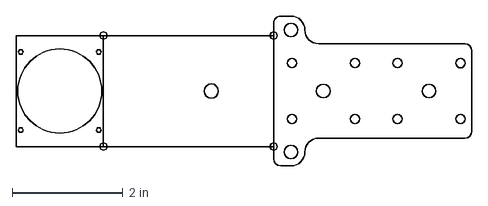
[picture p97: CAD file, 2014-10-29]
extruder_bracket.dxf
8.21 x 2.70 in
