jes1510/mendel_remix/belt_clamp.stl

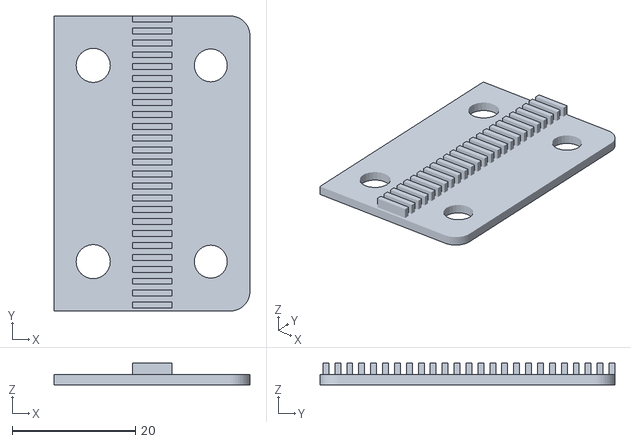
[picture p98: CAD file, 2014-10-29]
belt_clamp.stl
31.8 x 47.8 x 3.49
